codesmythe/KEMOJO/firmware/ps2.h

// ps2.h
// Copyright (c) 2023 Daniel Cliche
// SPDX-License-Identifier: MIT

#ifndef PS2_H
#define PS2_H

#include <stdint.h>

void ps2_pull_low(int pin);
void ps2_pull_high(int pin);

uint8_t ps2_read_byte(int clk_pin, int data_pin);
void ps2_write_byte(int clk_pin, int data_pin, uint8_t data);
// Return 1 of write timed out, or 0 if it did not.
int ps2_write_byte_with_timeout(int clk_pin, int data_pin, uint8_t data, unsigned long timeout);

#endif // PS2_H
